Wayne-Twinborn/Arkey/Resources/ArkeyCaps/ButtonCap.stl

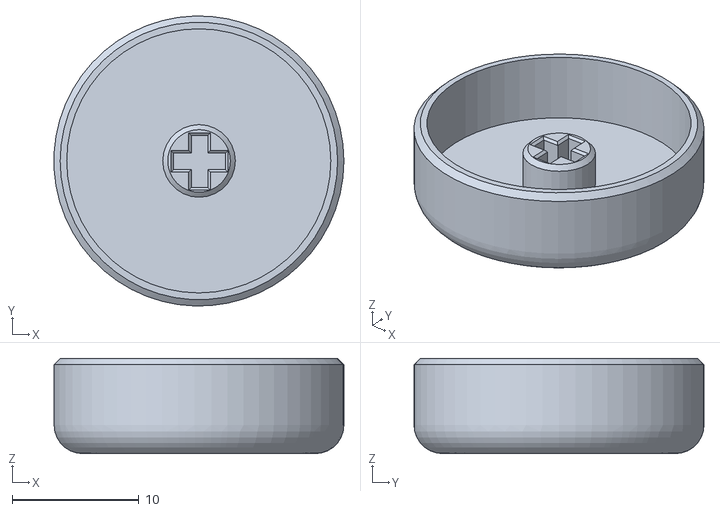
[picture p21: CAD file, 2023-09-21]
Resources/ArkeyCaps/ButtonCap.stl
22.8 x 22.8 x 7.50
