Wayne-Twinborn/Arkey/Resources/ArkeyCaps/v1-Keycap.stl

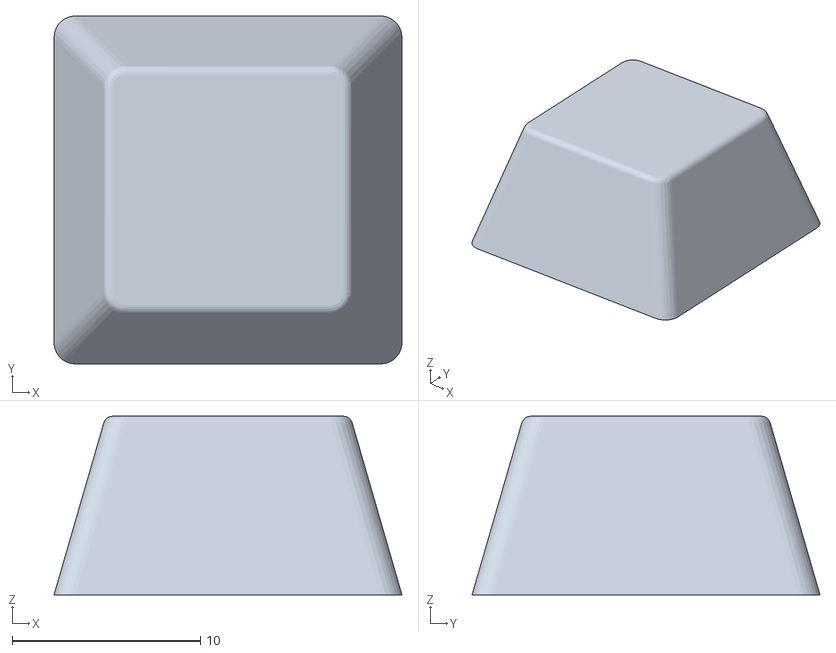
[picture p22: CAD file, 2023-08-29]
Resources/ArkeyCaps/v1-Keycap.stl
18.5 x 18.5 x 9.50
